CaptainDeathead/Nebulous/Console/cartridge_loader.py

import os
import sys
import tarfile
import logging
import importlib

try:
    import board
    import busio
    import digitalio
    import adafruit_sdcard
    TESTING = False
except:
    TESTING = True
    SpiDev = None
    logging.warning("No spidev module detected! Assuming this is a test!")

from shutil import rmtree
from io import BytesIO
from zipfile import ZipFile
from time import sleep
from math import ceil
from random import randint
from traceback import format_exc

# TODO: THIS IS ONLY FOR TESTING WITHOUT SD_CARDS IN THE PI
#TESTING = False

class CartridgeLoader:
    SD_BLOCK_SIZE = 512
    WRITE_STRIKES = 3

    def __init__(self, on_title_launch: object, flashing: bool = False) -> None:
        self.on_title_launch = on_title_launch
        self.flashing = flashing
        self.init_failure = False

        try:
            self.spi = busio.SPI(board.SCK, MOSI=board.MOSI, MISO=board.MISO)
            cs = digitalio.DigitalInOut(board.CE1)  # Commonly CE0 (GPIO8) or CE1 (GPIO7)
            self.sdcard = adafruit_sdcard.SDCard(self.spi, cs)

        except Exception as e:
            self.init_failure = True
            logging.error(f"Failed to initialize cartridge (sd) SPI interface!!! Error: {e}! Assuming this is a non-console test so continuing...")
            print(format_exc())

        self.write_strikes = self.WRITE_STRIKES
        self.last_connected_write = b'\x00'
        self.write_sd_block(2, self.last_connected_write)

    def is_sd_card_connected(self) -> bool:
        ret_val = True

        logging.info("Verifying SD is still connected...")

        sd_block_data = self.read_sd_block(2)
        sd_block_data += b'\x00'

        if sd_block_data[0] != self.last_connected_write[0]:
            logging.warning("No SD read response!")

            self.write_strikes -= 1

            if self.write_strikes == 0:
                ret_val = False
        else:
            self.write_strikes = self.WRITE_STRIKES

        self.last_connected_write = randint(1, 100).to_bytes()
        self.write_sd_block(2, self.last_connected_write)

        return ret_val

    def read_old_sd_block(self, block_num) -> bytes:
        try:
            # Read a block (512 bytes)
            block_data = bytearray(512)
            self.sdcard.readblocks(block_num, block_data)
            return block_data
        except Exception as e:
            print("Error reading SD block:", e)

    def read_sd_block(self, block_num) -> bytes:
        try:
            # Reuse block_data to avoid re-allocating a new bytearray each time
            if not hasattr(self, '_block_data'):
                self._block_data = bytearray(512)  # Create it only once

            # Read the block data
            self.sdcard.readblocks(block_num, self._block_data)
            
            # Return a slice of the bytearray to ensure immutability if needed
            return bytes(self._block_data)

        except Exception as e:
            print("Error reading SD block:", e)
            return b''  # Return an empty byte string on error

    def write_sd_block(self, block_num, data):
        try:
            # Write data to a block (ensure it's 512 bytes)
            if len(data) > 512:
                print("Data is too large for one block (max 512 bytes)")
                return
            block_data = bytearray(512)
            block_data[:len(data)] = data
            self.sdcard.writeblocks(block_num, block_data)
        except Exception as e:
            print("Error writing SD block:", e)

    def read_sd_data(self, start_block, end_block):
        data = bytearray()
        
        # Loop through each block from start_block to end_block
        for block in range(start_block, end_block + 1):
            #print(block / end_block * 100)
            block_data = self.read_sd_block(block)
            data.extend(block_data)
        
        return bytes(data)

    def write_sd_data(self, start_block, data):
        sector_size = 512
        data_len = len(data)
        current_block = start_block
        index = 0

        while index < data_len: 
            # Calculate remaining data to write in the current sector
            remaining_space_in_sector = sector_size - (index % sector_size)
            data_to_write = data[index:index + remaining_space_in_sector]

            # Write data to the current block
            self.write_sd_block(current_block, data_to_write)
            
            # Move to the next block
            index += len(data_to_write)
            current_block += 1

        # If there's partial data left at the last block, fill the rest with blank
        if len(data) % sector_size != 0:
            remaining_blank = sector_size - (len(data) % sector_size)
            blank_data = bytes([0] * remaining_blank)
            self.write_sd_block(current_block, blank_data)

    def unzip_inmemory(self, zip_data: bytes) -> str:
        # Converts the zip_data into a "fake" file (filelike object)
        zip_buffer = BytesIO(zip_data)

        # Opens the zip from memory
        with ZipFile(zip_buffer, "r") as file_bundle:
            print(f"Files in zip: {file_bundle.namelist()}")

            extracted_files = {name: file_bundle.read(name) for name in file_bundle.namelist()}

        return extracted_files

    def strip_null(self, bytes_str: bytes) -> None:
        return bytes_str.replace(b'\x00', b'')

    def flash_game(self) -> None:
        game_name = input("Enter game name with no spaces or wierd characters: ")
        game_path = input("Enter path to .tar.xz of game: ")

        with open(game_path, "rb") as f:
            xz = f.read()

        self.write_sd_data(0, game_name.encode('utf-8'))
        self.write_sd_block(1, ceil(len(xz)/512).to_bytes(512))
        self.write_sd_data(3, xz)

        logging.info(f"Successfully flashed {game_name} to cartridge!")

    def unload_cartridge(self) -> None:
        logging.debug("Unloading cartridge...")

        try:
            if self.init_failure:
                logging.warning("No cartridge attatched, so no cartridge to unload!")
            else:
                self.spi.deinit()
        except Exception as e:
            logging.critical(f"Critical error while unloading cartridge via SPI! Error: {e}!")

    def load_error(self, *args) -> None:
        raise Exception("Cartridge load failure! Likely a syntax error.")

    def load_cartridge(self) -> None:
        if TESTING or 1:
            sys.path.append(os.path.join(os.path.dirname(__file__), '..'))

            try:
                #from Games.Pong.consolemain import ConsoleEntry
                from Games.Snither.consolemain import ConsoleEntry
                #from Games.Racer.consolemain import ConsoleEntry
                #from Games.ShapeRoyale.consolemain import ConsoleEntry
                #from Games.Meteors.consolemain import ConsoleEntry
                #from Games.Caliby.consolemain import ConsoleEntry
                #from Games.Blocky.consolemain import ConsoleEntry
                #from Games.SuperMario3.consolemain import ConsoleEntry
                #from Games.MicroMachines.consolemain import ConsoleEntry

                self.on_title_launch(ConsoleEntry)
                return
            except Exception as e:
                logging.error("Error while invoking cartridge! Likely a syntax error.")
                self.on_title_launch(self.load_error)

        if self.flashing:
            self.flash_game()

        zip_data = b""

        game_name = self.strip_null(self.read_sd_block(0)).decode()
        xz_length = int.from_bytes(self.read_sd_block(1))

        logging.info(f"Loading {game_name} from cartridge...")

        zip_data = self.read_sd_data(3, xz_length+3)

        tmp_game_path = f"/tmp/Games/{game_name}"

        if not os.path.exists('tmp/Games'):
            logging.debug("Cartridge already has an entry in /tmp! Removing it...")
            rmtree('/tmp/Games', ignore_errors=True)
        
        os.makedirs(tmp_game_path)

        with open(f'{tmp_game_path}/e.tar.xz', 'wb') as f:
            f.write(zip_data)

        xz_buffer = BytesIO(zip_data)

        logging.debug("Extracting .tar.xz file into new /tmp directory...")
        with tarfile.open(fileobj=xz_buffer, mode='r:xz') as tar:
            tar.extractall(path='/tmp/Games')

        sys.path.append('/tmp') # Makes all the files in there discoverable.
        sys.path.append(os.path.join(os.path.dirname(__file__), '..'))
        
        logging.info("Invoking ConsoleEntry from consolemain in the unzipped game...")
        try:
            consolemain = importlib.import_module(f"Games.{game_name}.consolemain")
        except:
            raise Exception("Failed to import ConsoleEntry from consolemain!")

        try:
            self.on_title_launch(consolemain.ConsoleEntry)
        except Exception as e:
            import traceback
            traceback.print_exc()
            logging.warning(f"Cartridge finished or crashed! Exit MSG: {e}")
